JackDesBwa/Leoke/kicad/leoke.sch

## KiCad design kicad/leoke.sch (2014-01-12)

Schematic: leoke.sch

Parts:
C1, C2: 100nF
C3_1, C3_2, C5_1, C5_2: 22µF
Ccap1: 1µF
Cd1, Cd2, Cd3, Cd4, Cd5: 100nF
Cq1, Cq2: 22pF
Cref1: 100nF
Crst1: 100nF
Cusb1: 10µF
D1, D2: DIODE
Dcmp1: DIODE
F1: POLYFUSE
LED1: LED
P1, P2, P4, P5, P7: CONN_8
P3, P8: CONN_2
P6: CONN_3X2
PWR_D1: LED
Q1: 16MHz
Q2: PMOS
R1, R2, R3, R5: 560
R4, R6, R7: 10k
RX_D1: LED
Rboot1: 10k
Rpad1, Rpad2, Rpad3, Rpad4, Rpad5, Rpad6, Rpad7, Rpad8, Rpad9, Rpad10, Rpad11, Rpad12, Rpad13, Rpad14, Rpad15, Rpad16, Rpad17, Rpad18, Rpad19, Rpad20, Rpad21, Rpad22, Rpad23, Rpad24, Rpad25: 22M
Rrst1: 10k
Rusb1, Rusb2: 22
S1, S2, S3, S4, S5, S6, S7, S8, S9, S10, S11, S12, S13, S14, S15, S16, S17, S18, S19, S20, S21, S22, S23, S24, S25: PAD
TX_D1: LED
U1: ATMEGA32U4
U2: LM324
U3: REGU5V
U4: REGU3V3
USB1: MICROUSB
