JackDesBwa/Leoke/arduino/hardware/Leoke_arduino106/cores/arduino/MIDIUSB.cpp

#include "USBAPI.h"
#include "USBDesc.h"
#include "MIDIUSB.h"

#if defined(USBCON)
#ifdef MIDI_ENABLED

#define WEAK __attribute__ ((weak))

#define CLASS_AUDIO 0x01
#define SUBCLASS_AUDIO_CONTROL 0x01
#define SUBCLASS_MIDISTREAMING 0x03

#define TYPE_CS_INTERFACE 0x24
#define SUBTYPE_HEADER 0x01
#define SUBTYPE_MIDI_IN_JACK 0x02
#define SUBTYPE_MIDI_OUT_JACK 0x03
#define JACK_EMBEDDED 0x01
#define JACK_EXTERNAL 0x02

#define JACK1 0x01
#define JACK2 0x02
#define JACK3 0x03
#define JACK4 0x04

extern const ACDescriptor _acInterface PROGMEM;
const ACDescriptor _acInterface =
{
	D_INTERFACE(AC_INTERFACE,0,CLASS_AUDIO,SUBCLASS_AUDIO_CONTROL,0),
	{9, TYPE_CS_INTERFACE, SUBTYPE_HEADER, 0x0100, 9, 0x01, MIDI_INTERFACE}
};

int WEAK AC_GetInterface(u8* interfaceNum)
{
	interfaceNum[0] += 1;	// uses 1
	return USB_SendControl(TRANSFER_PGM,&_acInterface,sizeof(_acInterface));
}

extern const MIDIDescriptor _midiInterface PROGMEM;
const MIDIDescriptor _midiInterface =
{
	D_INTERFACE(MIDI_INTERFACE,MIDI_ENDPOINT_COUNT,CLASS_AUDIO,SUBCLASS_MIDISTREAMING,0),
	{7, TYPE_CS_INTERFACE, SUBTYPE_HEADER, 0x0100, 34},
	{6, TYPE_CS_INTERFACE, SUBTYPE_MIDI_IN_JACK, JACK_EMBEDDED, JACK1, 0x00},
	{9, TYPE_CS_INTERFACE, SUBTYPE_MIDI_OUT_JACK, JACK_EMBEDDED, JACK2, 1, JACK3, 1, 0x00},
    {6, TYPE_CS_INTERFACE, SUBTYPE_MIDI_IN_JACK, JACK_EXTERNAL, JACK3, 0x00},
    {9, TYPE_CS_INTERFACE, SUBTYPE_MIDI_OUT_JACK, JACK_EXTERNAL, JACK4, 1, JACK1, 1, 0x00},
    {
        D_ENDPOINT(USB_ENDPOINT_OUT(MIDI_ENDPOINT_OUT), USB_ENDPOINT_TYPE_BULK, 0x0040, 0x00),
        { 5, 0x25, 0x01, 0x01, JACK1 }
    },
    { 
        D_ENDPOINT(USB_ENDPOINT_IN(MIDI_ENDPOINT_IN), USB_ENDPOINT_TYPE_BULK, 0x0040, 0x00),
        { 5, 0x25, 0x01, 0x01, JACK2 }
    }
};


int WEAK MIDI_GetInterface(u8* interfaceNum)
{
	interfaceNum[0] += 1;	// uses 1
	return USB_SendControl(TRANSFER_PGM,&_midiInterface,sizeof(_midiInterface));
}

bool WEAK MIDI_Setup(Setup& setup)
{
    u8 r = setup.bRequest;
    u8 requestType = setup.bmRequestType;
    
    return false;
}

const MIDIEvent MIDI_EVENT_NONE = {0, 0, 0, 0};


void MIDIUSB_::accept(void) 
{
    midi_buffer *buffer = &(this->_rx_buffer);
    int i = (unsigned int)(buffer->head+1) % MIDI_BUFFER_SIZE;
    
    // if we should be storing the received character into the location
    // just before the tail (meaning that the head would advance to the
    // current location of the tail), we're about to overflow the buffer
    // and so we don't write the character or advance the head.

    // while we have room to store a byte
    while (i != buffer->tail) {
        int c = USB_Recv(MIDI_RX);
        if (c == -1)
            break;  // no more data
        buffer->buffer[buffer->head] = c;
        buffer->head = i;

        i = (unsigned int)(buffer->head+1) % MIDI_BUFFER_SIZE;
    }
}

int MIDIUSB_::available(void)
{
    midi_buffer *buffer = &(this->_rx_buffer);
    return ((unsigned int)(MIDI_BUFFER_SIZE + buffer->head - buffer->tail) % MIDI_BUFFER_SIZE) / 4;
}

MIDIEvent MIDIUSB_::peek(void)
{
    if(this->available() < 1) {
        return MIDI_EVENT_NONE;
    } else {
        midi_buffer *buffer = &(this->_rx_buffer);
        MIDIEvent result;
        result.type = buffer->buffer[buffer->tail];
        result.m1 = buffer->buffer[(buffer->tail+1) % MIDI_BUFFER_SIZE];
        result.m2 = buffer->buffer[(buffer->tail+2) % MIDI_BUFFER_SIZE];
        result.m3 = buffer->buffer[(buffer->tail+3) % MIDI_BUFFER_SIZE];
        return result;
    }
}

MIDIEvent MIDIUSB_::read(void)
{
    MIDIEvent event = this->peek();
    midi_buffer *buffer = &(this->_rx_buffer);
    buffer->tail = (unsigned int)(buffer->tail + 4) % MIDI_BUFFER_SIZE;
    return event;
}

void MIDIUSB_::flush(void)
{
    USB_Flush(MIDI_TX);
}

size_t MIDIUSB_::write(MIDIEvent c)
{
    // TODO: only try to send bytes if the connection is open
    if(USB_Ready(MIDI_TX)) {
        int r = USB_Send(MIDI_TX,&c,4);
        if (r > 0) {
            return r;
        } else {
            return 0;
        }
    } else {
        return 0;
    }
}

// This operator is a convenient way for a sketch to check whether the
// port has actually been configured and opened by the host (as opposed
// to just being connected to the host).  It can be used, for example, in 
// setup() before printing to ensure that an application on the host is
// actually ready to receive and display the data.
MIDIUSB_::operator bool() {
    return USB_Ready(MIDI_TX);
}

bool MIDIUSB_::note(bool on, MidiNote note, MidiOctave octave, MidiChannel channel, char velocity) {
    MIDIEvent evt = {0x08 | on, 0x80 | (on << 4) | channel, note + octave, velocity};
    return (MIDIUSB.write(evt) == sizeof(evt));
}

MIDIUSB_ MIDIUSB;


#endif
#endif
